sci-bots/teensy-3.2-clone.kicad/png/T32_ref-B.Cu.png

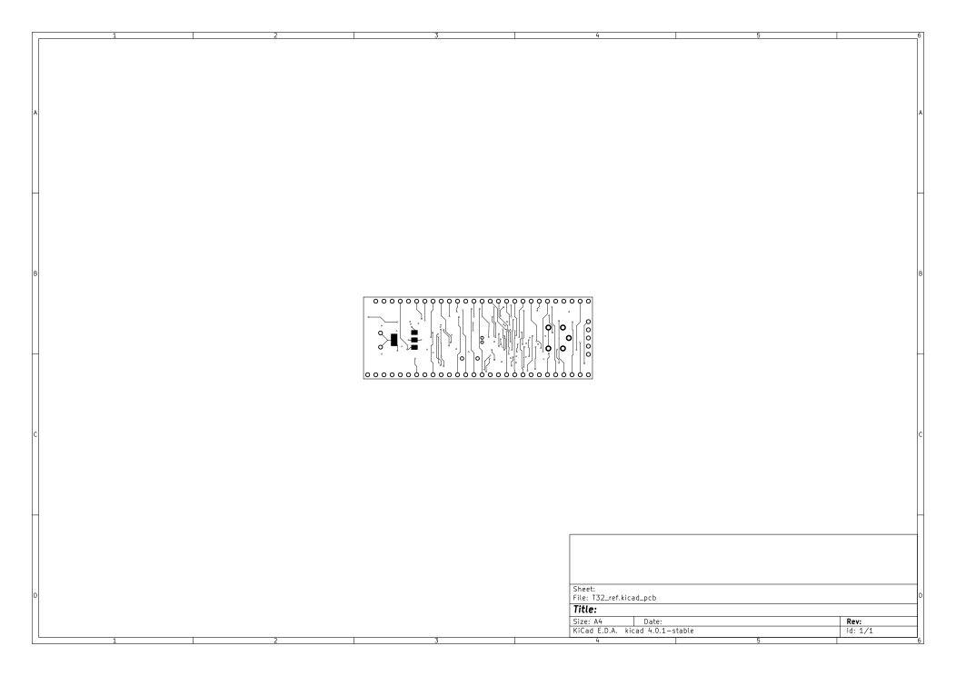
png/T32_ref-B.Cu.png
