sci-bots/teensy-3.2-clone.kicad/png/T32_ref-Edge.Cuts.png

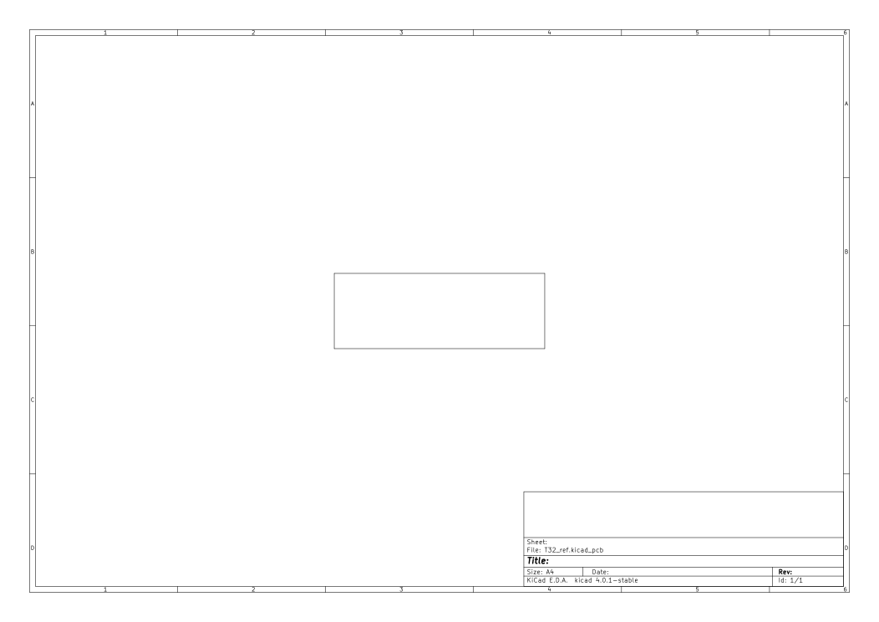
png/T32_ref-Edge.Cuts.png
