sci-bots/teensy-3.2-clone.kicad/pdf/T32_ref-In2.Cu.pdf

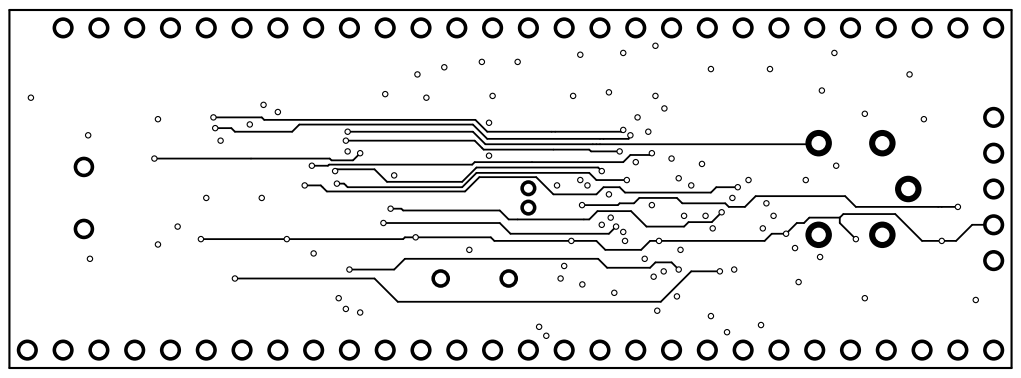
[picture p17: page 1]
