sci-bots/teensy-3.2-clone.kicad/pdf/T32_ref.pdf

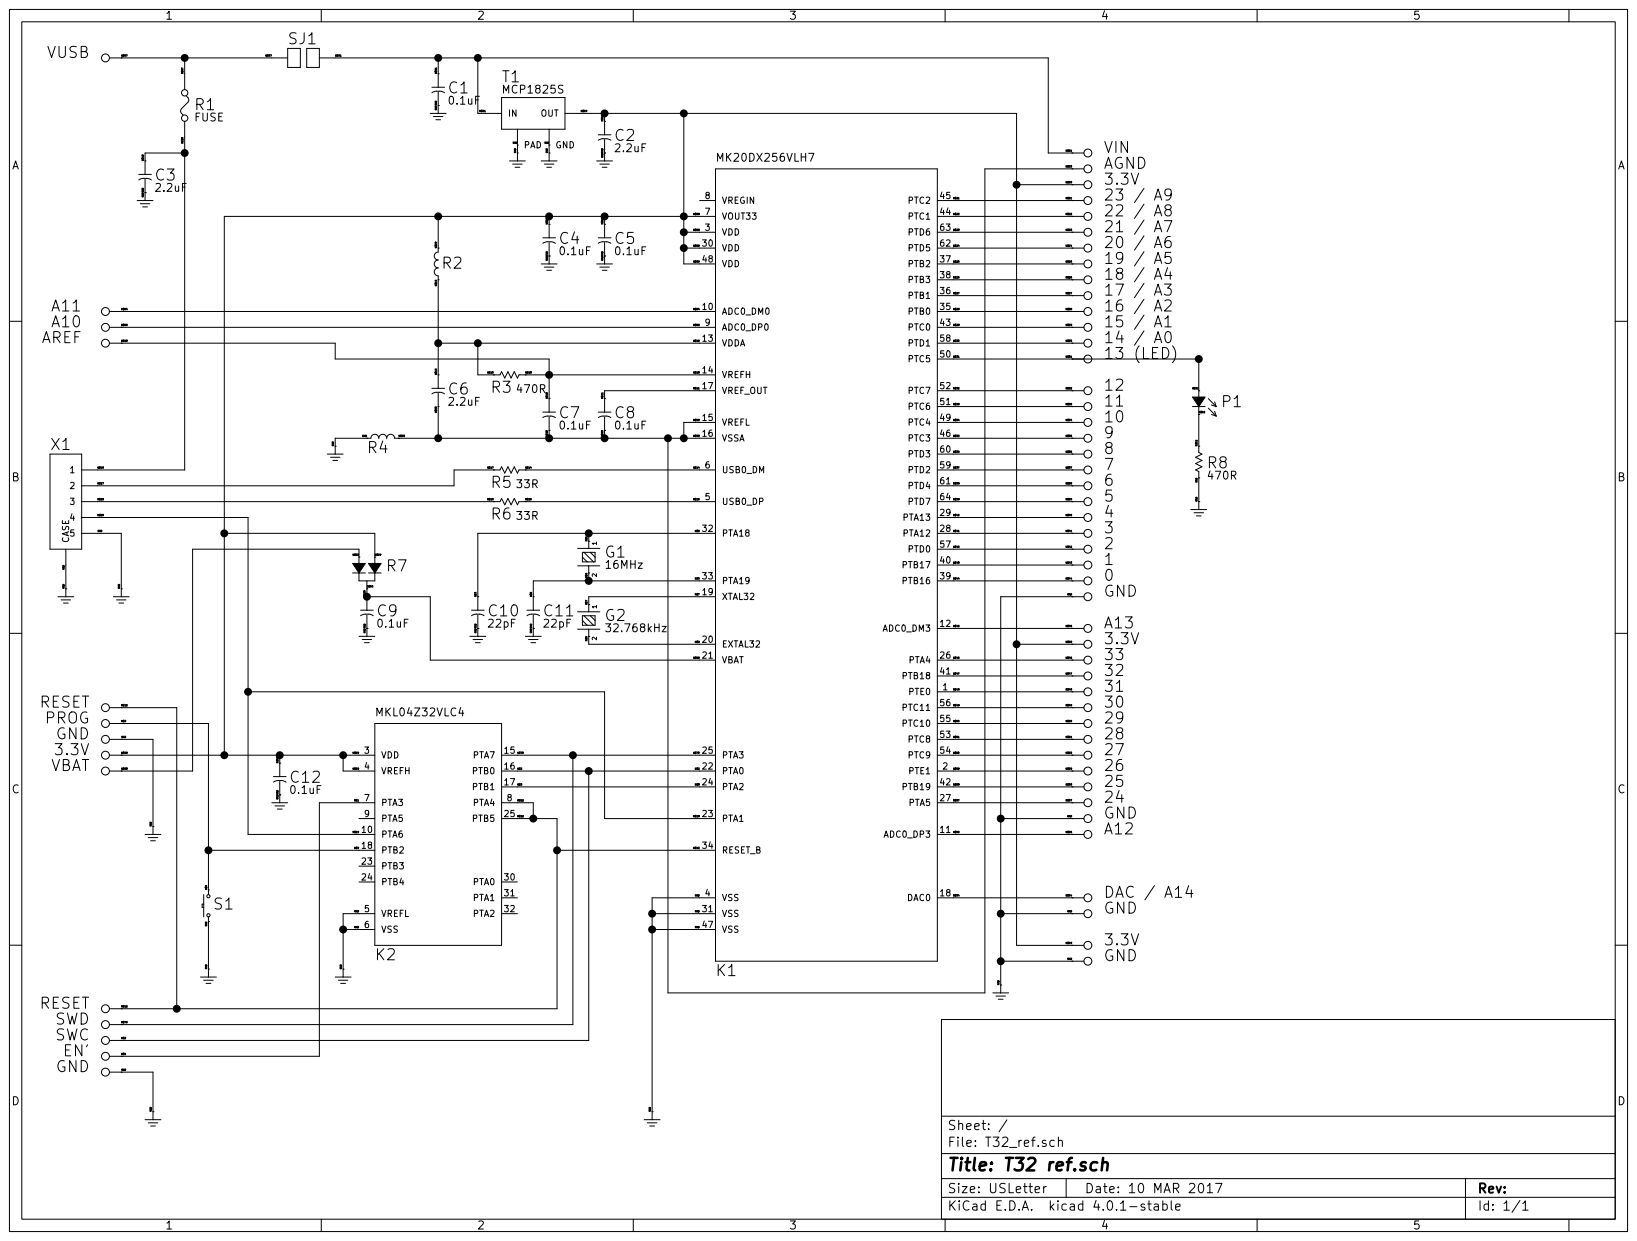
[picture p18: page 1]
